ericsims/8B/Hardware/Backplane/Mechanical/Backplane.step

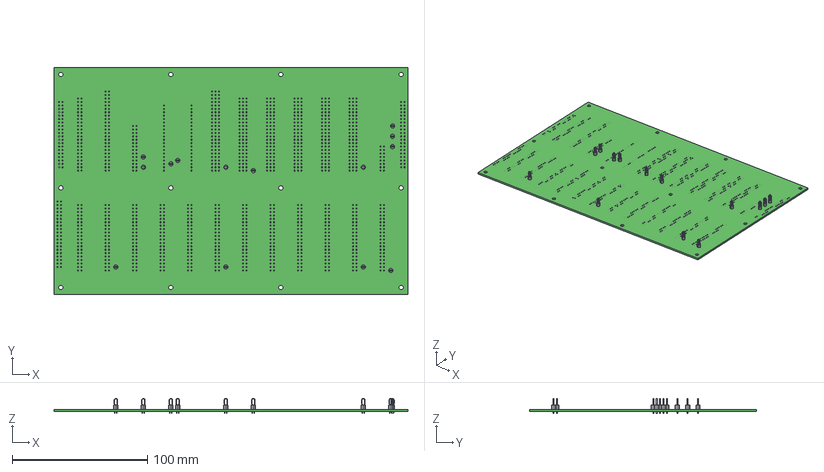
[picture p2: CAD file, 2022-09-18]
Hardware/Backplane/Mechanical/Backplane.step
261.6 x 167.6 x 11.3 mm
keystone-PN5011 x 14
