ericsims/8B/Mechanical/front/Frame.FCStd

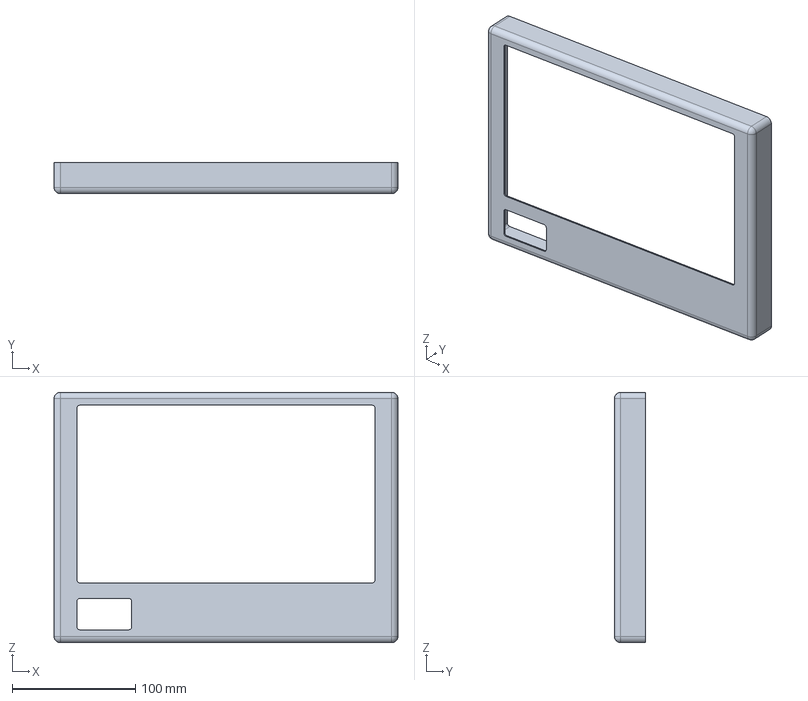
[picture p15: CAD file, 2026-02-22]
Mechanical/front/Frame.FCStd
279.4 x 25.4 x 203.2 mm
