ericsims/8B/Mechanical/vendor_models/E-500.IGS

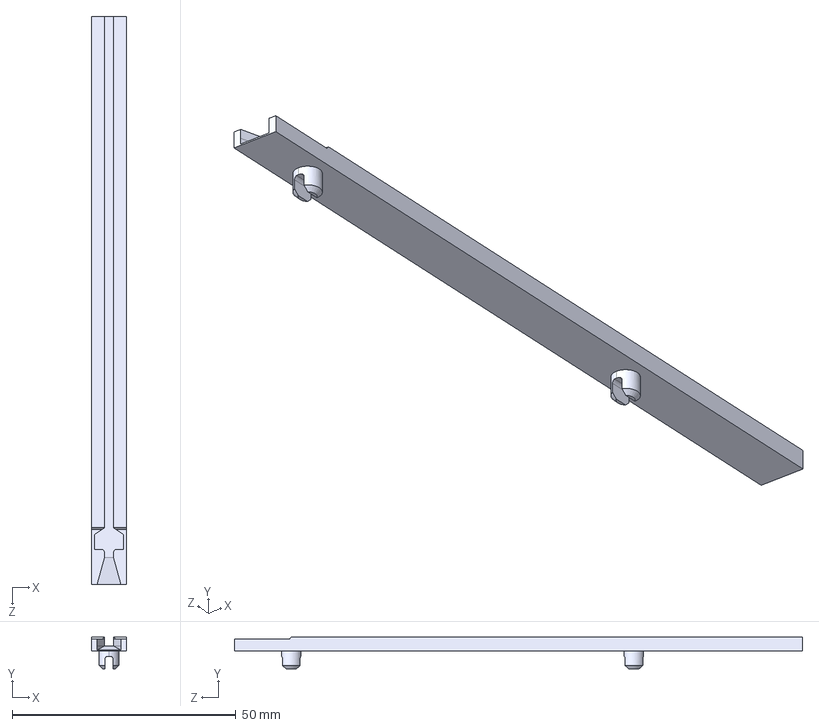
[picture p16: CAD file, 2026-02-06]
Mechanical/vendor_models/E-500.IGS
7.87 x 7.14 x 127.0 mm
