ericsims/8B/Hardware/ic-dip-packages-with-sockets-in-pitch-7-62mm-1.snapshot.2/DIP-32 W7.62mm IC with Socket.stp

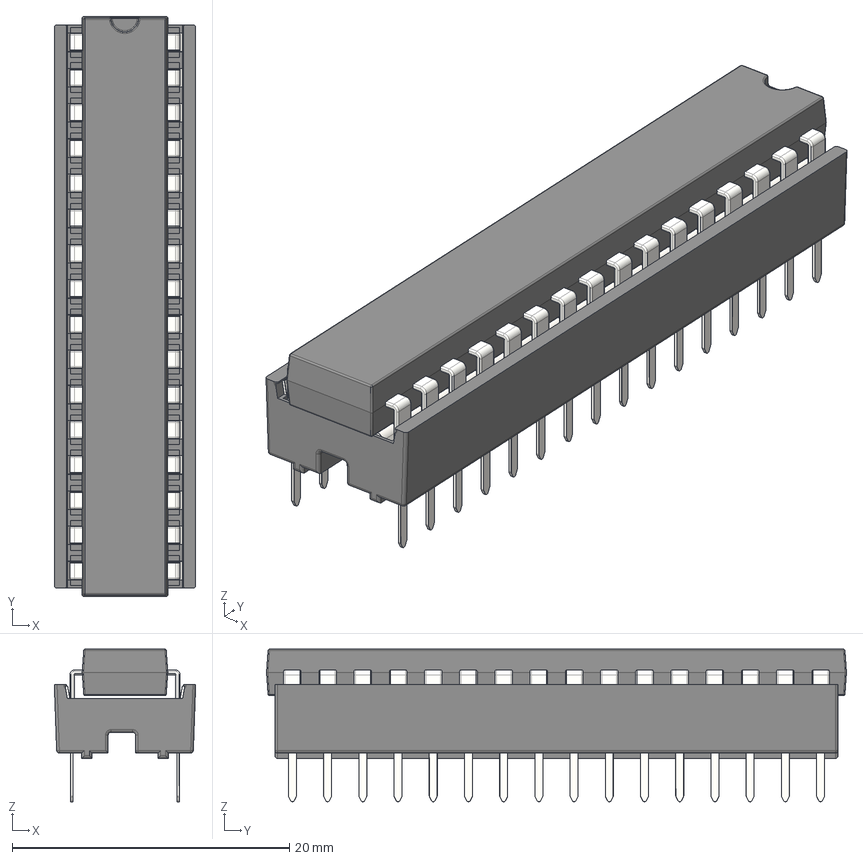
[picture p17: CAD file, 2021-09-13]
Hardware/ic-dip-packages-with-sockets-in-pitch-7-62mm-1.snapshot.2/DIP-32 W7.62mm IC with Socket.stp
10.2 x 41.8 x 11.0 mm
Stamped Dual Wipe Contact for DIP Sockets x 32
Body DIP-48 Socket
IC Beinchen x 32
DIP-32 W7.62
