ericsims/8B/Mechanical/card_cage/side_cage.FCStd

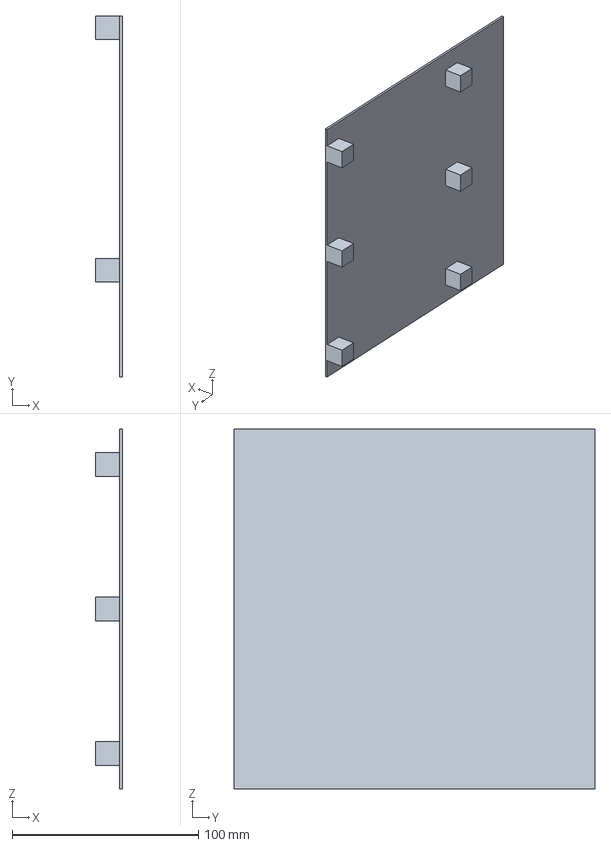
[picture p18: CAD file, 2026-02-14]
Mechanical/card_cage/side_cage.FCStd
14.2 x 193.5 x 193.0 mm
