ericsims/8B/Mechanical/front/bezel.FCStd

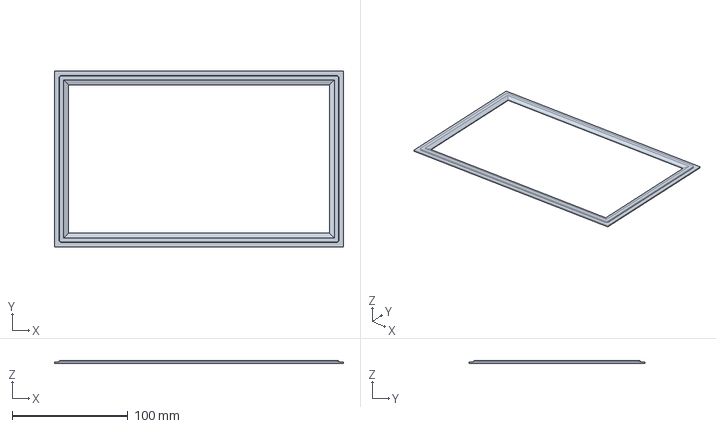
[picture p19: CAD file, 2026-02-22]
Mechanical/front/bezel.FCStd
250.2 x 152.4 x 2.54 mm
