ericsims/8B/Hardware/ic-dip-packages-with-sockets-in-pitch-7-62mm-1.snapshot.2/DIP-6 W7.62mm IC with Socket.stp

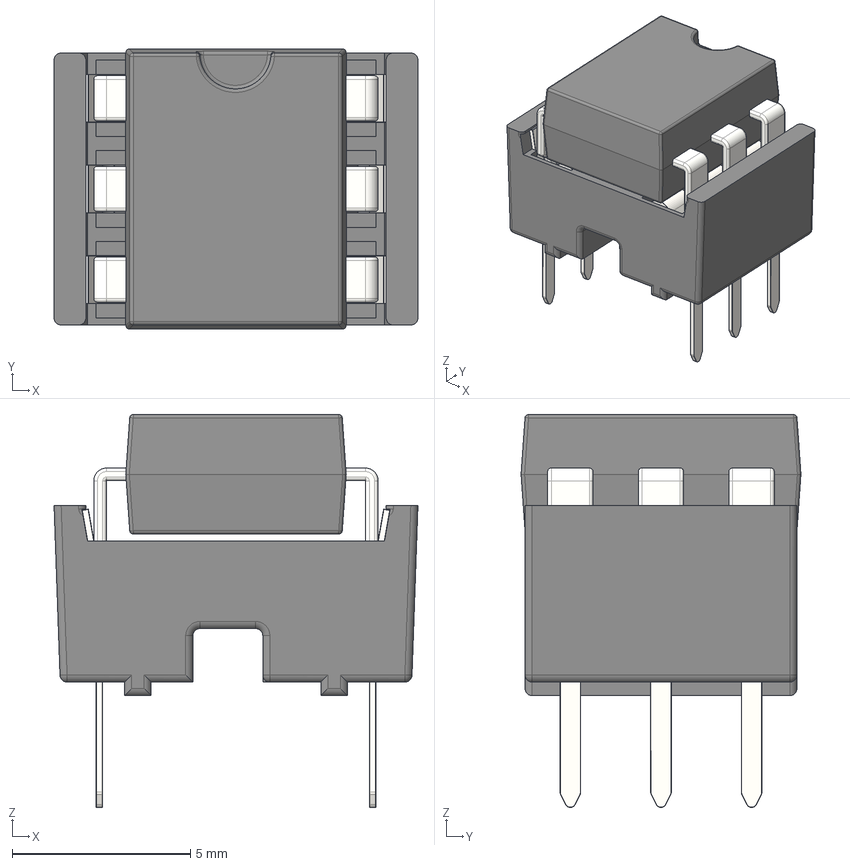
[picture p20: CAD file, 2021-09-13]
Hardware/ic-dip-packages-with-sockets-in-pitch-7-62mm-1.snapshot.2/DIP-6 W7.62mm IC with Socket.stp
10.2 x 7.85 x 11.0 mm
Stamped Dual Wipe Contact for DIP Sockets x 6
Body DIP-6 P7.62mm Socket
IC Beinchen x 6
DIP-6 W7.62
