ericsims/8B/Mechanical/card_cage/Essentra_R110710-062.FCStd

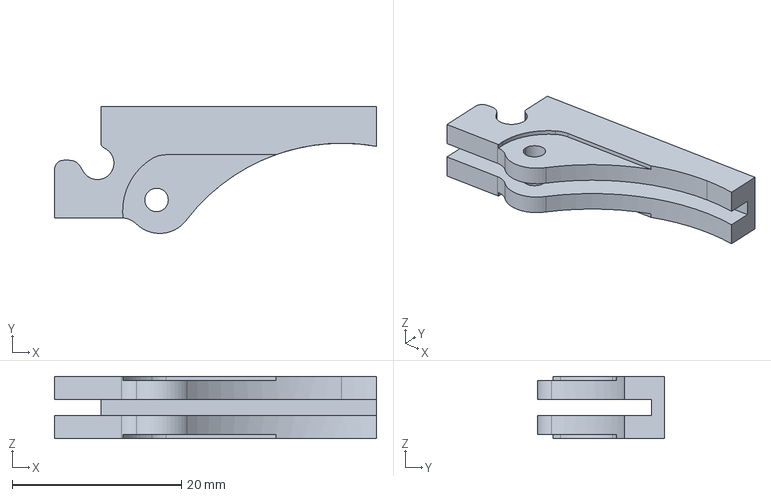
[picture p21: CAD file, 2026-02-06]
Mechanical/card_cage/Essentra_R110710-062.FCStd
38.1 x 15.0 x 7.37 mm
