ericsims/8B/Hardware/ic-dip-packages-with-sockets-in-pitch-7-62mm-1.snapshot.2/DIP-4 W7.62mm IC with Socket.stp

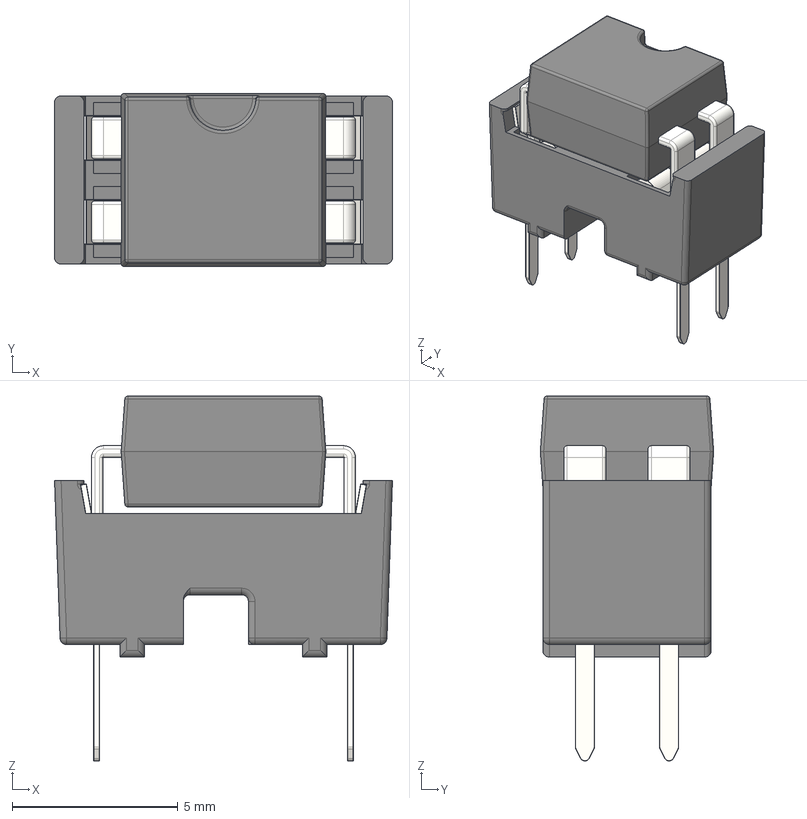
[picture p23: CAD file, 2021-09-13]
Hardware/ic-dip-packages-with-sockets-in-pitch-7-62mm-1.snapshot.2/DIP-4 W7.62mm IC with Socket.stp
10.2 x 5.23 x 11.0 mm
Stamped Dual Wipe Contact for DIP Sockets x 4
Body DIP-4 P7.62mm Socket
IC Beinchen x 4
DIP-4 W7.62
