ericsims/8B/Hardware/ic-dip-packages-with-sockets-in-pitch-7-62mm-1.snapshot.2/DIP-12 W7.62mm IC with Socket.stp

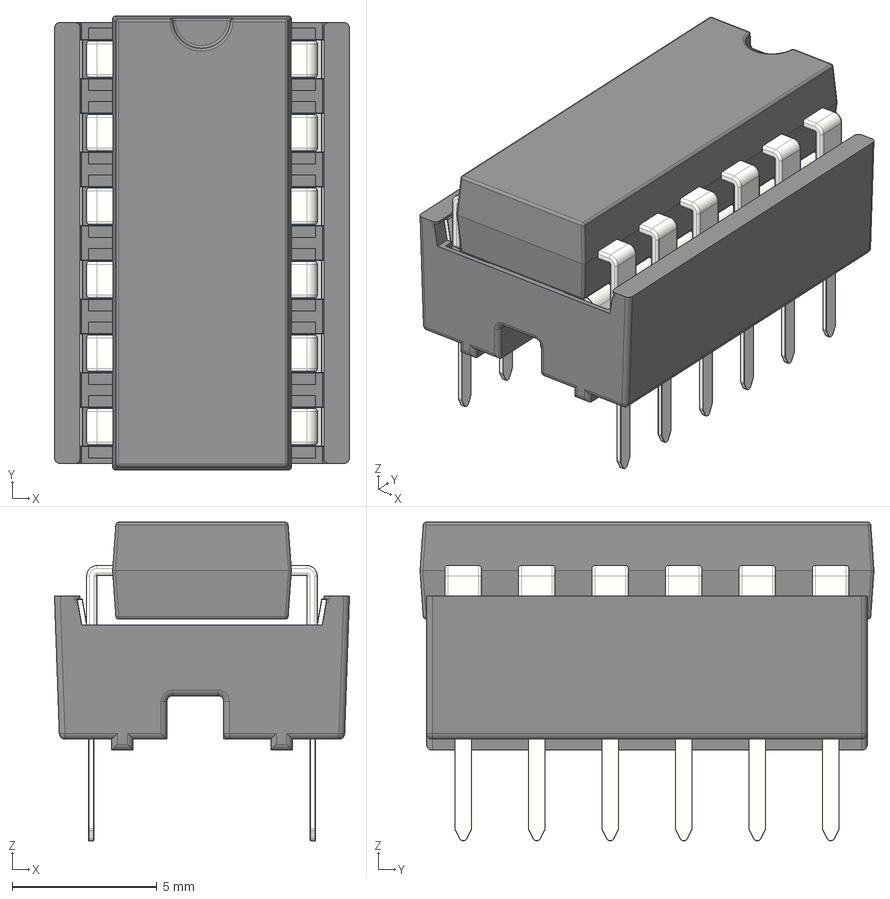
[picture p24: CAD file, 2021-09-13]
Hardware/ic-dip-packages-with-sockets-in-pitch-7-62mm-1.snapshot.2/DIP-12 W7.62mm IC with Socket.stp
10.2 x 15.7 x 11.0 mm
Stamped Dual Wipe Contact for DIP Sockets x 12
Body DIP-12 P7.62mm Socket
IC Beinchen x 12
DIP-12 W7.62
