ericsims/8B/Hardware/ic-dip-packages-with-sockets-in-pitch-7-62mm-1.snapshot.2/DIP-14 W7.62mm IC with Socket.stp

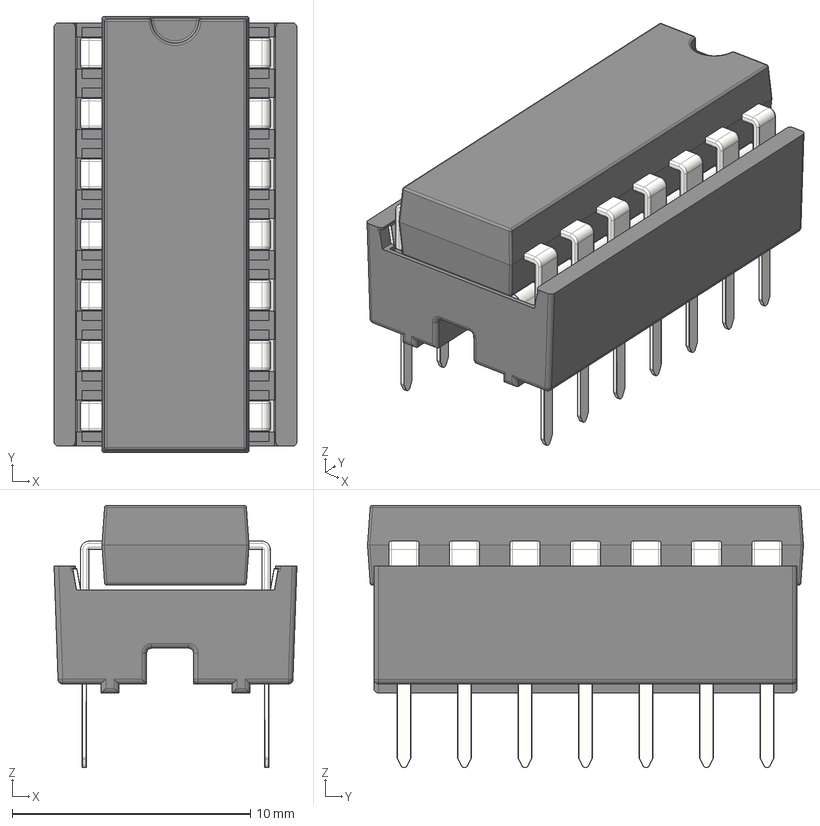
[picture p26: CAD file, 2021-09-13]
Hardware/ic-dip-packages-with-sockets-in-pitch-7-62mm-1.snapshot.2/DIP-14 W7.62mm IC with Socket.stp
10.2 x 18.3 x 11.0 mm
Stamped Dual Wipe Contact for DIP Sockets x 14
Body DIP-14 P7.62mm Socket
IC Beinchen x 14
DIP-14 W7.62
