ericsims/8B/Hardware/ic-dip-packages-with-sockets-in-pitch-7-62mm-1.snapshot.2/DIP-16 W7.62mm IC with Socket.stp

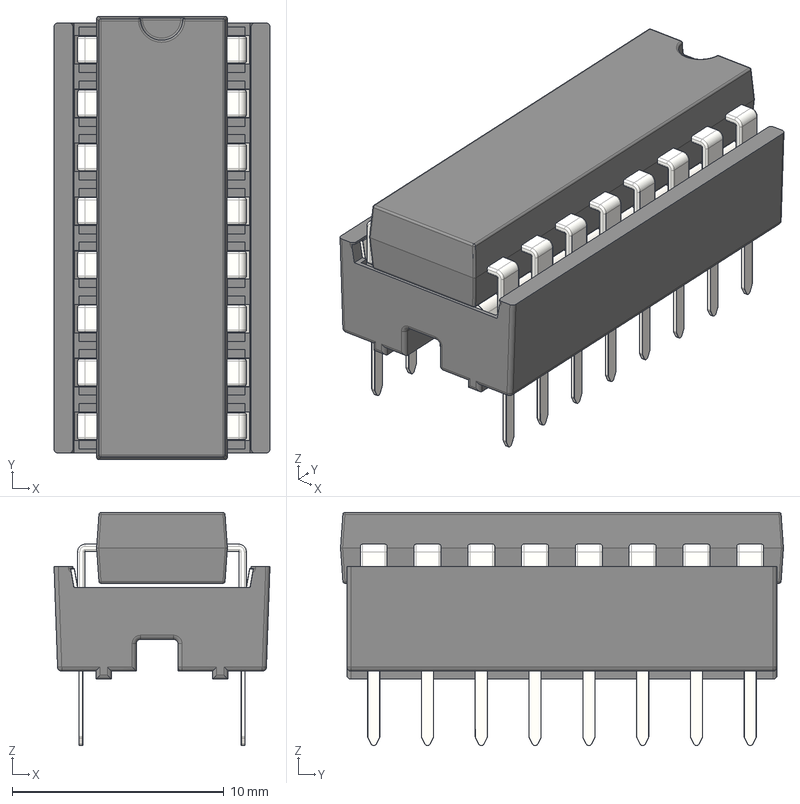
[picture p27: CAD file, 2021-09-13]
Hardware/ic-dip-packages-with-sockets-in-pitch-7-62mm-1.snapshot.2/DIP-16 W7.62mm IC with Socket.stp
10.2 x 20.9 x 11.0 mm
Stamped Dual Wipe Contact for DIP Sockets x 16
Body DIP-16 P7.62mm Socket
IC Beinchen x 16
DIP-16 W7.62
