ericsims/8B/Hardware/ic-dip-packages-with-sockets-in-pitch-7-62mm-1.snapshot.2/DIP-10 W7.62mm IC with Socket.stp

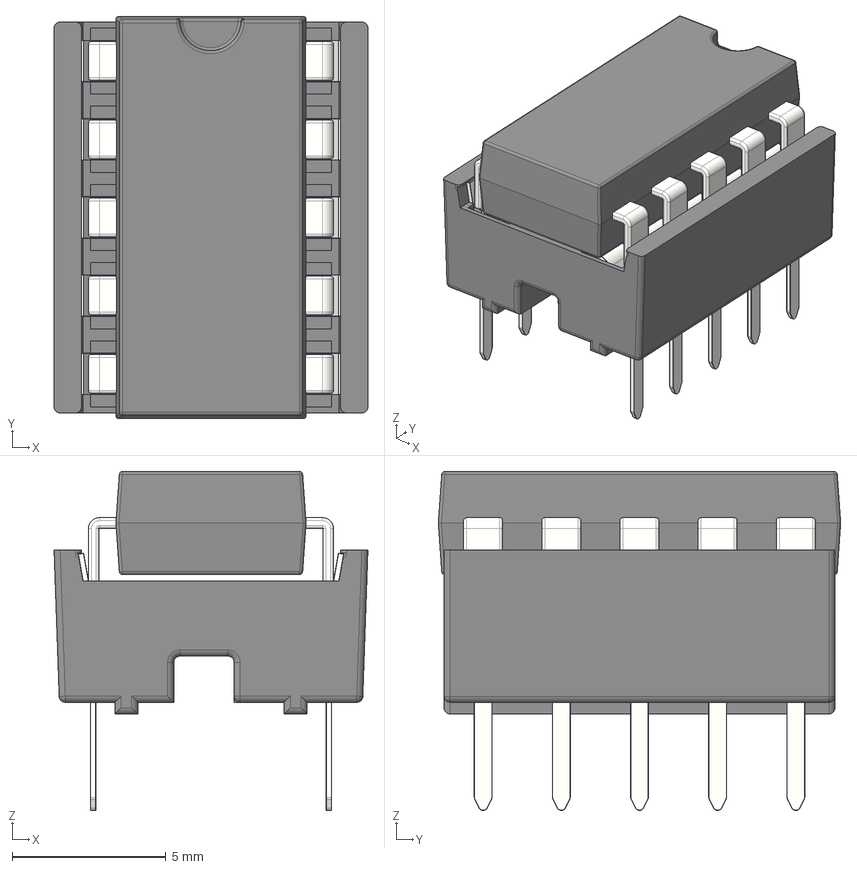
[picture p30: CAD file, 2021-09-13]
Hardware/ic-dip-packages-with-sockets-in-pitch-7-62mm-1.snapshot.2/DIP-10 W7.62mm IC with Socket.stp
10.2 x 13.1 x 11.0 mm
Stamped Dual Wipe Contact for DIP Sockets x 10
Body DIP-10 P7.62mm Socket
IC Beinchen x 10
DIP-10 W7.62
