ericsims/8B/Hardware/EE Sims/WE.asc

A1: inv; Vhigh=5 td=5n
A2: inv; Vhigh=5 td=5n
A3: inv; Vhigh=5 td=5n
C1: cap; 100p
R1: res; 1k
V1: voltage; PULSE(0 5 0 1n 1n {0.5/fck} {1/fck})
Named nets: 0, WE#
.param fck=1e6
.tran {3/fck}
