ericsims/8B/Hardware/sim/addr_decode.asc

U1: 74hc193
U2: 74hc138
U3: 74hc04
U4: 74hc138
U5: 74hc04
U6: 74hc04
U7: 74hc04
U8: 74hc04
U9: 74hc04
U10: 74hc04
U11: 74hc04
U12: 74hc04
U13: 74hc04
U14: 74hc04
U15: 74hc04
V1: voltage; 5
V2: voltage; PULSE(0 5 10u 1n 1n 10u 20u)
Named nets: 0, vcc, an0, an1, an2, EN0#, EN1#, EN2#, EN3#, EN4#, EN5#, EN6#, EN7#, an4, EN8#, EN9#, EN10#, EN11#, EN12#, EN13#, EN14#, EN15#, EN1, EN2, EN3, EN4, EN5, EN6, EN7, EN8, EN9, EN10, EN11, EN12
.tran 310u
.param tdgate=10n tdgate2=3*tdgate tripdtgate=1n vhighgate=5v vlowgate=0v
