ericsims/8B/Hardware/sim/UART1.asc

U1: 74hc193
U2: 74hc193
U3: 74hc138
U4: 74hc138
U5: 74hc374
U6: 74hc374
V1: voltage; 5
V2: voltage; PULSE(0 5 10u 1n 1n 10u 20u)
Named nets: 0, vcc, r0, r1, r2, w0, w1, w2, rn0#, rn1#, rn2#, rn3#, rn4#, rn5#, rn6#, rn7#, d0, d1, d2, d3, d4, d5, d6, d7, rd0, rd1, rd2, rd3, rd4, rd5, rd6, rd7, LOAD#, wn0#, wn1#, wn2#, wn3#, wn4#, wn5#, wn6#, wn7#
.tran 10m
.param tdgate=10n tdgate2=3*tdgate tripdtgate=1n vhighgate=5v vlowgate=0v
write pointer
read pointer
