ericsims/8B/Hardware/EE Sims/clock.asc

C1: cap; 250p
C2: cap; {cin}
C3: cap; {cin}
C4: cap; {cin}
C5: cap; {cin}
C6: cap; {cin}
C7: cap; {cin}
C8: cap; {cin}
C9: cap; {cin}
C10: cap; {cin}
C11: cap; {cin}
C12: cap; {cin}
C13: cap; {cin}
C14: cap; {cin}
C15: cap; {cin}
C16: cap; {cin}
C17: cap; {cin}
C18: cap; {cin}
C19: cap; {cin}
C20: cap; {cin}
C21: cap; {cin}
C22: cap; {cin}
C23: cap; {cin}
C24: cap; {cin}
C25: cap; {cin}
C26: cap; {cin}
C27: cap; {cin}
C28: cap; {cin}
C29: cap; {cin}
C30: cap; {cin}
C31: cap; {cin}
C32: cap; {cin}
C33: cap; {cin}
C34: cap; {cin}
C35: cap; {cin}
C36: cap; {cin}
C37: cap; {cin}
C38: cap; {cin}
C39: cap; {cin}
C40: cap; {cin}
C41: cap; {cin}
C42: cap; {cin}
C43: cap; {cin}
C44: cap; {cin}
C45: cap; {cin}
C46: cap; {cin}
C47: cap; {cin}
C48: cap; {cin}
C49: cap; {cin}
C50: cap; {cin}
C51: cap; {cin}
C52: cap; {cin}
C53: cap; {cin}
C54: cap; {cin}
C55: cap; {cin}
C56: cap; {cin}
C57: cap; {cin}
C58: cap; {cin}
C59: cap; {cin}
C60: cap; {cin}
C61: cap; {cin}
C62: cap; {cin}
C63: cap; {cin}
C64: cap; {cin}
C65: cap; {cin}
C66: cap; {cin}
C67: cap; {cin}
C68: cap; {cin}
C69: cap; {cin}
O1: ltline; clk1
O2: ltline; clk1
O3: ltline; clk1
O4: ltline; clk1
O5: ltline; clk1
O6: ltline; clk1
O7: ltline; clk1
O8: ltline; clk1
O9: ltline; clk1
O10: ltline; clk1
O11: ltline; clk1
O12: ltline; clk1
O13: ltline; clk1
O14: ltline; clk1
O15: ltline; clk1
O16: ltline; clk1
O17: ltline; clk1
O18: ltline; clk1
O19: ltline; clk1
O20: ltline; clk1
O21: ltline; clk1
O22: ltline; clk1
O23: ltline; clk1
O24: ltline; clk1
O25: ltline; clk1
O26: ltline; clk1
O27: ltline; clk1
O28: ltline; clk1
O29: ltline; clk1
O30: ltline; clk1
O31: ltline; clk1
O32: ltline; clk1
O33: ltline; clk1
O34: ltline; clk1
O35: ltline; clk1
O36: ltline; clk1
O37: ltline; clk1
O38: ltline; clk1
O39: ltline; clk1
O40: ltline; clk1
O41: ltline; clk1
O42: ltline; clk1
O43: ltline; clk1
O44: ltline; clk1
O45: ltline; clk1
O46: ltline; clk1
O47: ltline; clk1
O48: ltline; clk1
O49: ltline; clk1
O50: ltline; clk1
O51: ltline; clk1
O52: ltline; clk1
O53: ltline; clk1
O54: ltline; clk1
O55: ltline; clk1
O56: ltline; clk1
O57: ltline; clk1
O58: ltline; clk1
O59: ltline; clk1
O60: ltline; clk1
O61: ltline; clk1
O62: ltline; clk1
O63: ltline; clk1
O64: ltline; clk1
O65: ltline; clk1
O66: ltline; clk1
O67: ltline; clk1
O68: ltline; clk1
O69: ltline; clk1
O70: ltline; clk1
O71: ltline; clk1
O72: ltline; clk1
O73: ltline; clk1
O74: ltline; clk1
O75: ltline; clk1
O76: ltline; clk1
O77: ltline; clk1
O78: ltline; clk1
O79: ltline; clk1
O80: ltline; clk1
O81: ltline; clk1
O82: ltline; clk1
O83: ltline; clk1
O84: ltline; clk1
O85: ltline; clk1
O86: ltline; clk1
O87: ltline; clk1
O88: ltline; clk1
O89: ltline; clk1
O90: ltline; clk1
O91: ltline; clk1
O92: ltline; clk1
O93: ltline; clk1
O94: ltline; clk1
O95: ltline; clk1
O96: ltline; clk1
O97: ltline; clk1
O98: ltline; clk1
O99: ltline; clk1
O100: ltline; clk1
R1: res; 80
R3: res; 50
V1: voltage; PULSE(0 5 0.1u 1n 1n 0.5u 1u)
V2: voltage; 0.7
V3: voltage; 2
Named nets: 0, VIH, VIL
.tran 1u
.model clk ltra(R=4.857m C=1p L=18.6n Len=1)
.model clk1 ako:clk len=0.84
.model clk2 ako:clk len=1.34
.param rsource 150
;.step param rsource list 50 100 500
.param cin 3.5p
