ericsims/8B/Hardware/EE Sims/tone_detect.asc

B1: bv; V=V(in)*10
B2: bv; V=V(out)*10
C1: cap; {C}
C2: cap; {C}
C3: cap; {C}
C4: cap; {C}
C5: cap; 10µ
C6: cap; 4.7µ
C7: cap; 10µ
C8: cap; 4.7µ
D1: diode; 1N4148
D2: diode; 1N4148
D3: diode; 1N4148
D4: diode; 1N4148
R1: res; {R1}
R2: res; {R2}
R3: res; {R3}
R4: res; {R4}
R5: res; {R5}
R6: res; {R6}
R7: res; 10k
R8: res; 10k
U1: LM741
U2: LM741
V1: voltage; 15
V2: voltage; -15
V3: voltage; ""; wavefile="samp.wav" chan=0
Named nets: +15V, -15V, 0, in, out, vu_in, vu_out
.param C=0.1uF R1=1.7472156052756345k R2=0.04365726231035179k R3=4.963399532458674k R4=1.4497799629589634k R5=0.036225308395872874k R6=4.118459775995007k
.tran 2
.wave "in.wav" 16 44.1k V(in) V(in)
.wave "out.wav" 16 44.1k V(out) V(out)
