ericsims/8B/Hardware/EE Sims/Power Regulation.asc

C1: cap; 100µ
C2: cap; 0.1µ
C3: cap; 10µ
D1: zener; BZX84C6V2L
D2: diode; 1N4148
M1: nmos; BSB012N03MX3
Q1: npn; 2N3904
R1: res; 10
R2: res; 20m
R3: res; 383k
R4: res; 100k
R7: res; 2.2k
R8: res; 10k
R10: res; 220
U2: LT4256-3
V1: voltage; PWL(0 0 100u 12)
Named nets: 0, V_AUX
.tran 5m
