ericsims/8B/Hardware/TFT/Adafruit RA8875 TFT Breakout.sch

## EAGLE design Hardware/TFT/Adafruit RA8875 TFT Breakout.sch (2026-01-26)

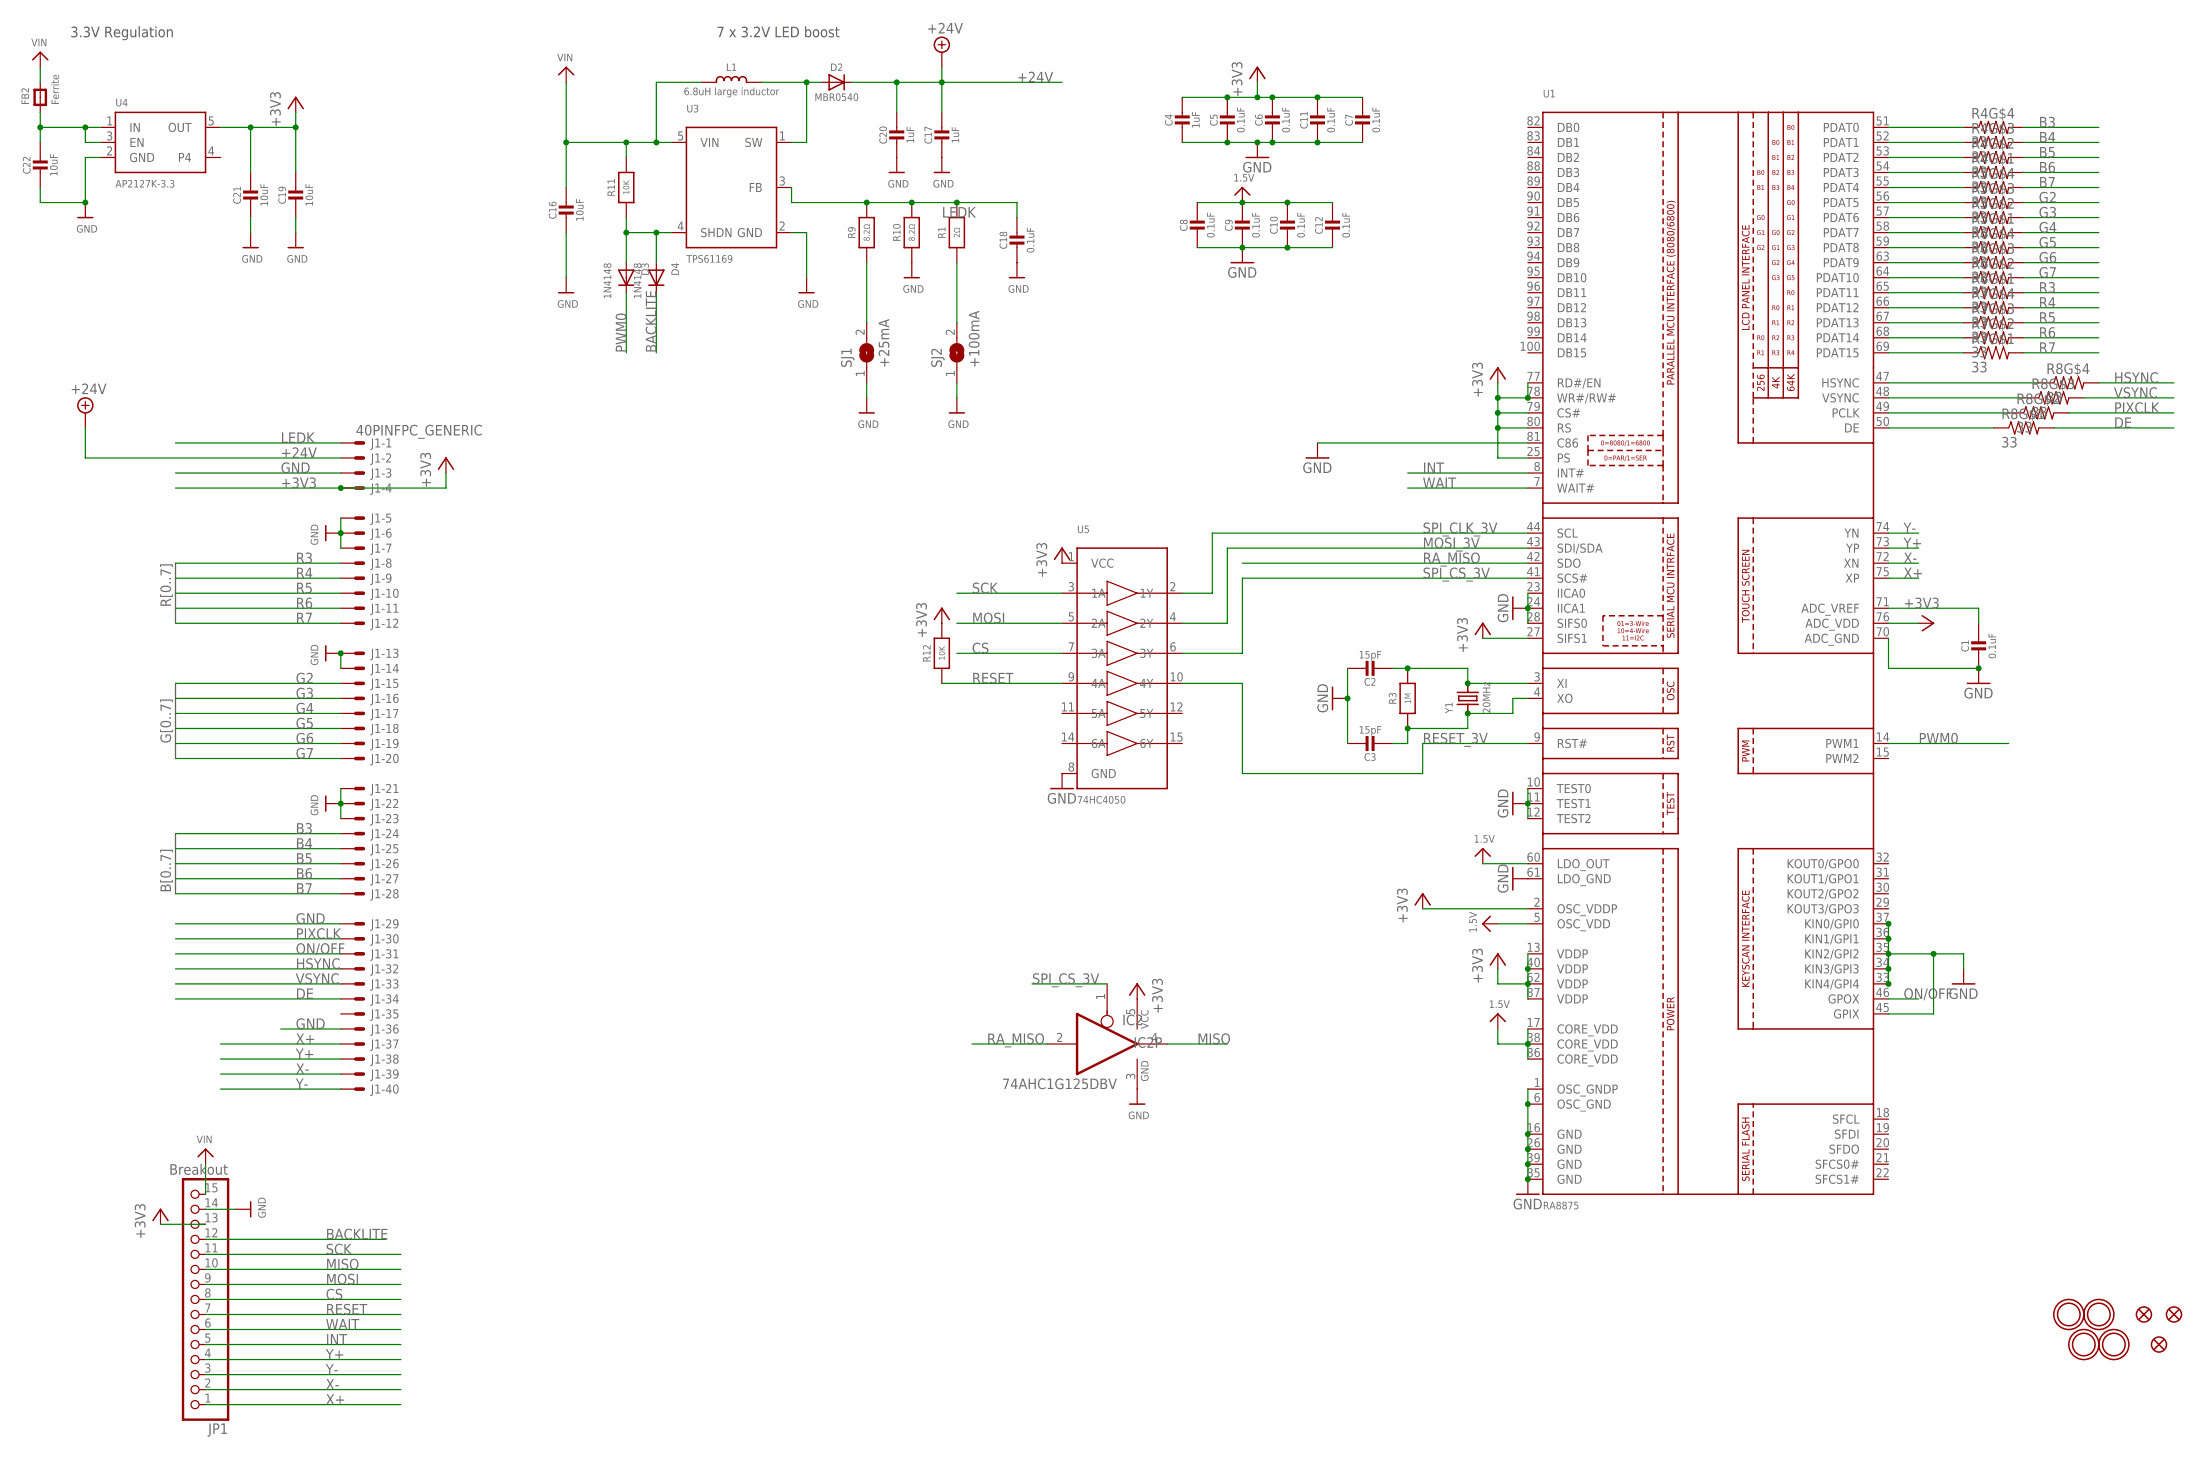
[picture p78: schematic Adafruit RA8875 TFT Breakout.sch]

Parts:
C1, C5, C6, C7, C8, C9, C10, C11, C12, C18: 0.1uF; 0603-NO
C2, C3: 15pF; 0603-NO
C4, C17, C20: 1uF; 0805-NO
C16, C19, C21, C22: 10uF; 0805-NO
D2: MBR0540; SOD-123
D3, D4: 1N4148; SOD-323_MINI
FB2: Ferrite; 0805-NO
FID1, FID2, FID3: FIDUCIAL_1MM
IC2: 74AHC1G125DBV; SOT23-5
J1: 40PINFPC_GENERIC; FPC_40
JP1: Breakout; 1X15-CB
L1: 6.8uH large inductor; INDUCTOR_5X5MM_NR5040_NOTHERMALS
R1: 2Ω; 0805-NO
R3: 1M; 0603-NO
R4, R5, R6, R7, R8: 33; RESPACK_4X0603
R9, R10: 8.2Ω; 0805-NO
R11, R12: 10K; 0603-NO
SJ1: +25mA; SOLDERJUMPER_ARROW_NOPASTE
SJ2: +100mA; SOLDERJUMPER_ARROW_NOPASTE
U1: RA8875; LQFP100
U3: TPS61169; SC70-5
U4: AP2127K-3.3; SOT23-5
U5: 74HC4050; TSSOP16
U$21, U$22, U$23, U$24: MOUNTINGHOLE2.5; MOUNTINGHOLE_2.5_PLATED
Y1: 20MHz; CRYSTAL_3.2X2.5

Connections:
1.5V: C8.1, C9.1, C10.1, C12.1, U1.5 (OSC_VDD), U1.17 (CORE_VDD), U1.38 (CORE_VDD), U1.60 (LDO_OUT), U1.86 (CORE_VDD)
+3V3: C4.1, C5.1, C6.1, C7.1, C11.1, C19.1, C21.1, IC2.5 (VCC), J1.4 (MS), JP1.13, R12.2, U1.2 (OSC_VDDP), U1.13 (VDDP), U1.25 (PS), U1.27 (SIFS1), U1.40 (VDDP), U1.62 (VDDP), U1.76 (ADC_VDD), U1.77 (RD#/EN), U1.78 (WR#/RW#), U1.79 (CS#), U1.80 (RS), U1.87 (VDDP), U4.5 (OUT), U5.1 (VCC)
+24V: C17.1, C20.1, D2.C, J1.2 (MS)
B3: J1.24 (MS), R4.5 (2)
B4: J1.25 (MS), R4.6 (2)
B5: J1.26 (MS), R4.7 (2)
B6: J1.27 (MS), R4.8 (2)
B7: J1.28 (MS), R5.5 (2)
BACKLITE: D4.C, JP1.12
CS: JP1.8, U5.7 (3A)
DE: J1.34 (MS), R8.8 (2)
G2: J1.15 (MS), R5.6 (2)
G3: J1.16 (MS), R5.7 (2)
G4: J1.17 (MS), R5.8 (2)
G5: J1.18 (MS), R6.5 (2)
G6: J1.19 (MS), R6.6 (2)
G7: J1.20 (MS), R6.7 (2)
GND: C1.2, C2.1, C3.1, C4.2, C5.2, C6.2, C7.2, C8.2, C9.2, C10.2, C11.2, C12.2, C16.2, C17.2, C18.2, C19.2, C20.2, C21.2, C22.2, IC2.3 (GND), J1.3 (MS), J1.5 (MS), J1.6 (MS), J1.7 (MS), J1.13 (MS), J1.14 (MS), J1.21 (MS), J1.22 (MS), J1.23 (MS), J1.29 (MS), J1.36 (MS), JP1.14, R10.1, SJ1.1, SJ2.1, U1.1 (OSC_GNDP), U1.6 (OSC_GND), U1.10 (TEST0), U1.11 (TEST1), U1.12 (TEST2), U1.16 (GND), U1.23 (IICA0), U1.24 (IICA1), U1.26 (GND), U1.28 (SIFS0), U1.33 (KIN4/GPI4), U1.34 (KIN3/GPI3), U1.35 (KIN2/GPI2), U1.36 (KIN1/GPI1), U1.37 (KIN0/GPI0), U1.39 (GND), U1.45 (GPIX), U1.61 (LDO_GND), U1.70 (ADC_GND), U1.81 (C86), U1.85 (GND), U3.2 (GND), U4.2 (GND), U5.8 (GND)
HSYNC: J1.32 (MS), R8.5 (2)
INT: JP1.5, U1.8 (INT#)
LEDK: C18.1, J1.1 (MSV), R1.2, R9.2, R10.2, U3.3 (FB)
MISO: IC2.4 (O), JP1.10
MOSI: JP1.9, U5.5 (2A)
MOSI_3V: U1.43 (SDI/SDA), U5.4 (2Y)
unnamed: D2.A, L1.P$2 (2), U3.1 (SW)
unnamed: C2.2, R3.2, U1.3 (XI), Y1.2
unnamed: C1.1, U1.71 (ADC_VREF)
unnamed: R4.4 (1), U1.51 (PDAT0)
unnamed: R4.3 (1), U1.52 (PDAT1)
unnamed: R4.2 (1), U1.53 (PDAT2)
unnamed: R4.1, U1.54 (PDAT3)
unnamed: R5.4 (1), U1.55 (PDAT4)
unnamed: R5.3 (1), U1.56 (PDAT5)
unnamed: R5.2 (1), U1.57 (PDAT6)
unnamed: R5.1, U1.58 (PDAT7)
unnamed: R6.4 (1), U1.59 (PDAT8)
unnamed: R6.3 (1), U1.63 (PDAT9)
unnamed: R6.2 (1), U1.64 (PDAT10)
unnamed: R6.1, U1.65 (PDAT11)
unnamed: R7.4 (1), U1.66 (PDAT12)
unnamed: R7.3 (1), U1.67 (PDAT13)
unnamed: R7.2 (1), U1.68 (PDAT14)
unnamed: R7.1, U1.69 (PDAT15)
unnamed: R8.1, U1.50 (DE)
unnamed: R8.2 (1), U1.49 (PCLK)
unnamed: R8.3 (1), U1.48 (VSYNC)
unnamed: R8.4 (1), U1.47 (HSYNC)
unnamed: R9.1, SJ1.2
unnamed: C22.1, FB2.1, U4.1 (IN), U4.3 (EN)
unnamed: R1.1, SJ2.2
unnamed: C3.2, R3.1, U1.4 (XO), Y1.1
ON/OFF: J1.31 (MS), U1.46 (GPOX)
PIXCLK: J1.30 (MS), R8.7 (2)
PWM0: D3.C, U1.14 (PWM1)
R3: J1.8 (MS), R6.8 (2)
R4: J1.9 (MS), R7.5 (2)
R5: J1.10 (MS), R7.6 (2)
R6: J1.11 (MS), R7.7 (2)
R7: J1.12 (MS), R7.8 (2)
RA_MISO: IC2.2 (I), U1.42 (SDO)
RESET: JP1.7, R12.1, U5.9 (4A)
RESET_3V: U1.9 (RST#), U5.10 (4Y)
SCK: JP1.11, U5.3 (1A)
SHDN: D3.A, D4.A, R11.1, U3.4 (SHDN)
SPI_CLK_3V: U1.44 (SCL), U5.2 (1Y)
SPI_CS_3V: IC2.1 (OE), U1.41 (SCS#), U5.6 (3Y)
VIN: C16.1, FB2.2, JP1.15, L1.P$1 (1), R11.2, U3.5 (VIN)
VSYNC: J1.33 (MS), R8.6 (2)
WAIT: JP1.6, U1.7 (WAIT#)
X+: J1.37 (MS), JP1.1, U1.75 (XP)
X-: J1.39 (MS), JP1.2, U1.72 (XN)
Y+: J1.38 (MS), JP1.4, U1.73 (YP)
Y-: J1.40 (MS), JP1.3, U1.74 (YN)

Notes on the sheet:
7 x 3.2V LED boost
3.3V Regulation
