ericsims/8B/Software/apps/hello1.asm

; program entry
#bank rom
top:
init_pointers:
    loadw sp, #STACK_BASE
    storew #0x0000, BP

main:
    storew #str_1, static_uart_print.data_pointer
    call static_uart_print

    halt

; constants
str_1: #d "hello world!\n\0"

; includes
#include "../src/CPU.asm"
#include "../src/lib/char_utils.asm"

; global vars
#bank ram
STACK_BASE: #res 0
