ericsims/8B/Software/tests/1210_test_math_mult16.asm

; program entry
#bank rom
top:
init_pointers:
    loadw sp, #STACK_BASE
    storew #0x0000, BP

test:
    alloc 4 ; res
    pushw #0x0000 ; x
    pushw #0x0000 ; y
    call mult16
    dealloc 4 ; x,y
    popw hl
    assert hl, #0x0000
    popw hl
    assert hl, #0x0000

    alloc 4
    pushw #0x7FFF
    pushw #0x7FFF
    call mult16
    dealloc 4
    popw hl
    assert hl, #(0x7FFF*0x7FFF)&0xFFFF
    popw hl
    assert hl, #(0x7FFF*0x7FFF)>>16

    alloc 4
    pushw #-32768
    pushw #-32768
    call mult16
    dealloc 4
    popw hl
    assert hl, #(-32768*-32768)&0xFFFF
    popw hl
    assert hl, #(-32768*-32768)>>16

    alloc 4
    pushw #-32768
    pushw #32767
    call mult16
    dealloc 4
    popw hl
    assert hl, #(-32768*32767)&0xFFFF
    popw hl
    assert hl, #(-32768*32767)>>16

    alloc 4
    pushw #32767
    pushw #-32768
    call mult16
    dealloc 4
    popw hl
    assert hl, #(32767*-32768)&0xFFFF
    popw hl
    assert hl, #(32767*-32768)>>16

    alloc 4
    pushw #-1
    pushw #-1
    call mult16
    dealloc 4
    popw hl
    assert hl, #(-1*-1)&0xFFFF
    popw hl
    assert hl, #(-1*-1)>>16

    alloc 4
    pushw #-1
    pushw #32767
    call mult16
    dealloc 4
    popw hl
    assert hl, #(-1*32767)&0xFFFF
    popw hl
    assert hl, #(-1*32767)>>16

    alloc 4
    pushw #-1
    pushw #-32768
    call mult16
    dealloc 4
    popw hl
    assert hl, #(-1*-32768)&0xFFFF
    popw hl
    assert hl, #(-1*-32768)>>16

    alloc 4
    pushw #12345
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
    call mult16
    dealloc 4
    popw hl
    assert hl, #(-123*-456)&0xFFFF
    popw hl
    assert hl, #(-123*-456)>>16

    alloc 4
    pushw #25000
    pushw #-12345
    call mult16
    dealloc 4
    popw hl
    assert hl, #(25000*-12345)&0xFFFF
    popw hl
    assert hl, #(25000*-12345)>>16

    alloc 4
    pushw #-25000
    pushw #12345
    call mult16
    dealloc 4
    popw hl
    assert hl, #(-25000*12345)&0xFFFF
    popw hl
    assert hl, #(-25000*12345)>>16

    alloc 4
    pushw #300
    pushw #300
    call mult16
    dealloc 4
    popw hl
    assert hl, #(300*300)&0xFFFF
    popw hl
    assert hl, #(300*300)>>16

    alloc 4
    pushw #-300
    pushw #-300
    call mult16
    dealloc 4
    popw hl
    assert hl, #(-300*-300)&0xFFFF
    popw hl
    assert hl, #(-300*-300)>>16

    alloc 4
    pushw #-300
    pushw #300
    call mult16
    dealloc 4
    popw hl
    assert hl, #(-300*300)&0xFFFF
    popw hl
    assert hl, #(-300*300)>>16

    alloc 4
    pushw #0x7FFF
    pushw #-1
    call mult16
    dealloc 4
    popw hl
    assert hl, #(0x7FFF*-1)&0xFFFF
    popw hl
    assert hl, #(0x7FFF*-1)>>16

    alloc 4
    pushw #-32768
    pushw #-1
    call mult16
    dealloc 4
    popw hl
    assert hl, #(-32768*-1)&0xFFFF
    popw hl
    assert hl, #(-32768*-1)>>16

    halt


; includes
#include "../src/CPU.asm"
#include "../src/lib/lib_math.asm"

; global vars
#bank ram
STACK_BASE: #res 0
