ericsims/8B/Software/tests/1905_test_ra8876_draw_char.asm

; program entry
#bank rom
top:
init_pointers:
    loadw sp, #STACK_BASE
    storew #0x0000, BP

main:
    call ra8876_init
    assert b, #0

    pushw #0x0000 ; x
    pushw #0x0000 ; y
    pushw #TFT_SCREEN_WIDTH ; width
    pushw #TFT_SCREEN_HEIGHT ; height
    call ra8876_set_active_window_xywh
    dealloc 8

    
    ; fill background color
    pushw #0x0000 ; x
    pushw #0x0000 ; y
    pushw #TFT_SCREEN_WIDTH ; width
    pushw #TFT_SCREEN_HEIGHT ; height
    pushw #COLOR65K_GRAYSCALE10
    call ra8876_draw_sqaure_fill
    dealloc 10


    call ra8876_enable_text_mode

    
    pushw #COLOR65K_GRAYSCALE1
    call ra8876_set_background_color_16bpp
    dealloc 2

    pushw #COLOR65K_LIGHTGREEN
    call ra8876_set_foreground_color_16bpp
    dealloc 2
    
    pushw #15
    pushw #5
    call ra8876_set_text_cursor_pos
    dealloc 4
    

    call ra8876_set_text_size_16
    store #RA8876_MRWDP, RA8876_ADDR ; ram access
    store #"a", RA8876_DATA
    
    call ra8876_set_text_size_24
    store #RA8876_MRWDP, RA8876_ADDR ; ram access
    store #"b", RA8876_DATA

    call ra8876_text_chroma_key_enable
    call ra8876_set_text_size_32
    store #RA8876_MRWDP, RA8876_ADDR ; ram access
    store #"c", RA8876_DATA

    __load a, RA8876, RA8876_CCR1 ; Input Control Register
    and a, #!(3<<RA8876_CCR1_HEIGHT_SCALE_POS) ; clear bits
    or a, #(RA8876_CCR1_HEIGHT_SCALE_X2 << RA8876_CCR1_HEIGHT_SCALE_POS) ; set size bits
    __store a, RA8876, RA8876_CCR1

    store #RA8876_MRWDP, RA8876_ADDR ; ram access
    store #"d", RA8876_DATA


    halt

; includes
#include "../src/CPU.asm"
#include "../src/lib/lib_ra8876.asm"

; global vars
#bank ram
STACK_BASE: #res 1024
