ericsims/8B/Software/tests/1719_test_static_memcpy.asm

; program entry
#bank rom
top:
init_pointers:
    loadw sp, #STACK_BASE
    storew #0x0000, BP

main:

    storew #test_src, static_memcpy.src_ptr
    storew #test_dst, static_memcpy.dst_ptr
    storew #(test_src.end - test_src), static_memcpy.len
    call static_memcpy

    ; check result
    pushw #test_src
    pushw #test_dst
    call strcmp
    dealloc 4
    assert b, #0

    halt

; constants
test_src: #d "this is some test data made up of characters the total length is pretty long, but it is less than the 255 character limit for the xfr 8 instruction. Here are some more characters to add to the string. Oh and some numbers too 1234!\0"
    .end:

; includes
#include "../src/CPU.asm"
#include "../src/lib/char_utils.asm"

; global vars
#bank ram
test_dst: #res 256
STACK_BASE: #res 0
