ericsims/8B/Software/tests/1712_test_isdigit.asm

; program entry
#bank rom
top:
init_pointers:
    loadw sp, #STACK_BASE
    storew #0x0000, BP

main:
    push #"\0"
    call isdigit
    pop a
    assert b, #0
    
    push #"a"
    call isdigit
    pop a
    assert b, #0

    push #"/"
    call isdigit
    pop a
    assert b, #0

    push #"0"
    call isdigit
    pop a
    assert b, #1

    push #"1"
    call isdigit
    pop a
    assert b, #1

    push #"2"
    call isdigit
    pop a
    assert b, #1

    push #"3"
    call isdigit
    pop a
    assert b, #1

    push #"4"
    call isdigit
    pop a
    assert b, #1

    push #"5"
    call isdigit
    pop a
    assert b, #1

    push #"6"
    call isdigit
    pop a
    assert b, #1

    push #"7"
    call isdigit
    pop a
    assert b, #1

    push #"8"
    call isdigit
    pop a
    assert b, #1

    push #"9"
    call isdigit
    pop a
    assert b, #1

    push #":"
    call isdigit
    pop a
    assert b, #0
    
    halt

; includes
#include "../src/CPU.asm"
#include "../src/lib/char_utils.asm"

; global vars
#bank ram
STACK_BASE: #res 0
