ericsims/8B/Software/tests/0076_test_stack_dealloc.asm

;;
; @file
; @author Eric Sims
;
; @section Description
; tests deallocating bytes from stack
;
; @section Test Coverage
; @coverage dealloc
;
;;

; program entry
#bank rom
top:
    loadw sp, #STACK_BASE

    push #0x00
    push #0x11
    push #0x22
    push #0x33
    push #0x44
    push #0x55
    push #0x66
    push #0x77
    push #0x88
    push #0x99
    push #0xAA
    push #0xBB
    push #0xCC
    push #0xDD
    push #0xEE
    push #0xFF

    dealloc 0
    pop a
    assert a, #0xFF
    
    dealloc 1
    pop a
    assert a, #0xDD

    dealloc 2
    pop a
    assert a, #0xAA

    dealloc 8
    pop a
    assert a, #0x11

    halt

; constants
; -- none --

; includes
#include "../src/CPU.asm"

; global vars
#bank ram
DUMMY: #res 250
STACK_BASE: #res 0
