ericsims/8B/Software/tests/1201_test_math_mult8.asm

; program entry
#bank rom
top:
init_pointers:
    loadw sp, #STACK_BASE
    storew #0x0000, BP

test:
    push #{val_a}
    push #{val_b}
    pushw #sum
    call mult8
    dealloc 4

    loadw hl, sum

    assert hl, #(val_a*val_b)

    halt

; constants
val_a=0xFF
val_b=0xFF

; includes
#include "../src/CPU.asm"
#include "../src/lib/math.asm"

; global vars
#bank ram
sum: #res 2 ;result poitbed
STACK_BASE: #res 0
