ericsims/8B/Software/tests/0002_test_a_imm.asm

;;
; @file
; @author Eric Sims
;
; @section Description
; tests a register immedate loads
;
; @section Test Coverage
; @coverage load_a_imm
;
;;

; program entry
#bank rom
top:
    ; tests load a register with immediate value

    load a, #0x00
    assert a, #0x00 ; check that a reg is correct

    load a, #0x01
    assert a, #0x01 ; check that a reg is correct

    load a, #0xAA
    assert a, #0xAA ; check that a reg is correct

    load a, #0x55
    assert a, #0x55 ; check that a reg is correct

    load a, #0xFF
    assert a, #0xFF ; check that a reg is correct

    load a, #0x00
    assert a, #0x00 ; check that a reg is correct

    halt

; constants
; -- none --

; includes
#include "../src/CPU.asm"

; global vars
; -- none --
