ericsims/8B/Software/tests/0004_test_b_imm.asm

;;
; @file
; @author Eric Sims
;
; @section Description
; tests b register immedate loads
;
; @section Test Coverage
; @coverage load_b_imm
;
;;

; program entry
#bank rom
top:
    ; tests load b register with immediate value

    load b, #0x00
    assert b, #0x00 ; check that a reg is correct

    load b, #0x01
    assert b, #0x01 ; check that a reg is correct

    load b, #0xAA
    assert b, #0xAA ; check that a reg is correct

    load b, #0x55
    assert b, #0x55 ; check that a reg is correct

    load b, #0xFF
    assert b, #0xFF ; check that a reg is correct

    load b, #0x00
    assert b, #0x00 ; check that a reg is correct

    halt

; constants
; -- none --

; includes
#include "../src/CPU.asm"

; global vars
; -- none --
