ericsims/8B/Software/tests/0011_test_ab.asm

;;
; @file
; @author Eric Sims
;
; @section Description
; tests loading a register from b
;
; @section Test Coverage
; @coverage load_a_b load_b_a
;
;;

; program entry
#bank rom
    top:
    load a, #0x55
    load b, #0xAA
    load a, b
    assert a, #0xAA

    load a, #0xCC
    load b, a
    assert b, #0xCC

    halt

; constants
; -- none --

; includes
#include "../src/CPU.asm"

; global vars
; -- none --
