ericsims/8B/Software/tests/0072_test_stack_init.asm

;;
; @file
; @author Eric Sims
;
; @section Description
; tests initializing stack pointer
;
; @section Test Coverage
; @coverage loadw_sp_imm loadw_hl_sp
;
;;

; program entry
#bank rom
top:
    loadw sp, #STACK_BASE
    loadw hl, sp
    assert hl, #STACK_BASE

    halt

; constants
; -- none --

; includes
#include "../src/CPU.asm"

; global vars
#bank ram
STACK_BASE: #res 0
