ericsims/8B/Software/tests/1103_test_math_add32_static.asm

; program entry
#bank rom
top:
init_pointers:
    loadw sp, #STACK_BASE
    storew #0x0000, BP

test:
    storew #0x1234, static_x_32
    storew #0x5678, static_x_32+2

    storew #0xFFAD, static_y_32
    storew #0xBEEF, static_y_32+2

    call static_add32

    ; check result is 0x11E2_1567
    load a, static_z_32+3
    assert a, #0x67
    load a, static_z_32+2
    assert a, #0x15
    load a, static_z_32+1
    assert a, #0xE2
    load a, static_z_32
    assert a, #0x11
    load a, static_cf
    assert a, #0x01

    halt

; constants
; -- none --

; includes
#include "../src/CPU.asm"
#include "../src/lib/static_math.asm"

; global vars
#bank ram
STACK_BASE: #res 0
