ericsims/8B/Software/tests/1104_test_math_mult8_fast.asm

; program entry
#bank rom
top:
init_pointers:
    loadw sp, #STACK_BASE
    storew #0x0000, BP

test:
    storew #0x1234, static_x_32
    storew #0x5678, static_x_32+2

    call static_negate32


    ; check result is 0xEDCB_A988
    load a, static_x_32+3
    assert a, #0x88
    load a, static_x_32+2
    assert a, #0xA9
    load a, static_x_32+1
    assert a, #0xCB
    load a, static_x_32
    assert a, #0xED
    ; TODO: check carry flag

    halt

; constants
; -- none --

; includes
#include "../src/CPU.asm"
#include "../src/lib/static_math.asm"

; global vars
#bank ram
STACK_BASE: #res 0
