ericsims/8B/Software/tests/2004_test_nav_dijkstra.asm

#include "../src/CPU.asm"

#bank ram
path:
    #res (dijkstra.SIZE_OF_ARRAYS+1)

#bank rom
top:
main:
    init_pointers:
        loadw sp, #DEFAULT_STACK
        storew #0x0000, BP

    get_map:
        call print_map_name
 
    nav: ; 0 --> 1
        push #0x00
        push #0x01
        call dijkstra
        pop a
        pop a
    
    verify_result: ; [0, 7, 3, 9, 10, 11, 1]
        load a, {path+0}
        assert a, #0x00
        load a, {path+1}
        assert a, #0x07
        load a, {path+2}
        assert a, #0x03
        load a, {path+3}
        assert a, #0x09
        load a, {path+4}
        assert a, #0x0A
        load a, {path+5}
        assert a, #0x0B
        load a, {path+6}
        assert a, #0x01
        load a, {path+7}
        assert a, #0xFF

    end:
        halt
; end main



#include "../src/lib/map_utils.asm"
#include "../src/lib/nav_utils.asm"

map: #d inchexstr("../lib_dev/Localize/Maps/map.dat")
